bpbwaite/DistributedFenceMonitor/Data Package/Testing/Test Procedures/Board_Power_1.xlsx

Board Number (MKR 1310) | Status | Minimum Current(mA) | Maximum Current(mA) | Accelerometer | Voltage (V) | Current (mA)
A1 | OK | 18 | 111 | (ADXL) 1 | 3.3 | 0.0215
A2 | OK |  |  | (ADXL) 2 | 3.3 | 0.0215
A3 | OK |  |  | (ADXL) 3 | 3.3 | 0.0239
A4 | OK |  |  | (ADXL) 4 | 3.3 | 0.0226
 |  |  |  | (MPU) 5 | 3.3 | 2
 |  |  |  | (MPU) 6 | 3.3 | 1
Board Number (RP2040) |  | Baseline Current(mA) | Max Current(mA) | (MPU) 7 | 3.3 | 2
1 |  | 41 | 120
2 |  | 40 | 120
