bpbwaite/DistributedFenceMonitor/Data Package/Testing/Test Procedures/Capstone Testing Software.xlsx

Software Requirement | Code Portions | Location | Pass/Fail | Notes
setup_mkr1310() run | setup_mkr1310() | dfm_mkr1310.cpp | Pass | Serial.Prints worked and could be seen through the serial monitor
Maximum Scan Loops | while (++attackCounter <= MAXIMUM_SCANS) | dfm_mkr1310.cpp | Fail | Tested if the data collection loop would stop collecting after a set collection time of 10 seconds. Node would not break out of loop after continous motion.
Epoch Timing Test | next_wake_epoch, next_send_epoch | dfm_mkr1310.cpp, | Fail | Timing on each node was incorrect. Node 1 and 2 sent and woke up at the same time without waiting for one to send and the other not to send. Next phase is to calibrate Epoch with identifiers.
Maximum Scan Loops p2 | while (++attackCounter <= MAXIMUM_SCANS) | dfm_mkr1310.cpp | Pass | Added Inactivity in Data End Function that checks last 1/4 second of data and determines if collection should stop after 10 seconds or continue for another 10 seconds. Function caused loop to exit after 10 seconds and 20 seconds of collection
Severity Test | SeverityLevel | dfm_mkr1310.cpp | Fail | Nodes were returning 15 severity on every motion. No sensitivity abstraction from the nodes. This is likely due to the node always choosing the highest peak which is always going to be 15
Severity Test p2 | SeverityLevel=getFilteredSeverity) | dfm_mkr1310.cpp | Pass | After applying a FIR and utilizing a conv on the data, the severity level returned a more accurate severity level for each instance of motion. Calibration is done for FIR in setup. Severity was serial printed.
Motion Wakeup | if(motionDetected) | dfm_mkr1310.cpp | Pass | Final Test for ISR and the nodes wokeup for a motion detection. Successfully sent Serial Print indicating they were in collection mode and printed severity.
Timing Test p2. | next_wake_epoch, next_send_epoch | dfm_mkr1310.cpp | Pass | After applying an identifier with Epoch, each node waits 1 second after the previous node sent data to send theirs. Nodes sleep and wakeup based on their identifier.
