bpbwaite/DistributedFenceMonitor/Data Package/Testing/Test Procedures/Waterproofing Standard.pdf

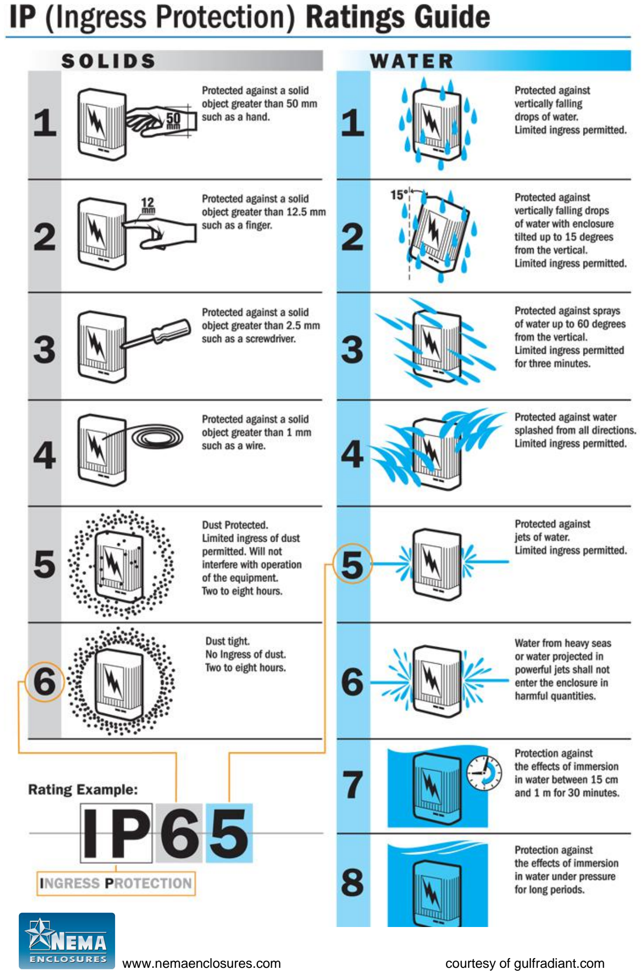
[picture p20: page 1]

www.nemaenclosures.com | courtesy of gulfradiant.com
