bpbwaite/DistributedFenceMonitor/Data Package/Testing/on_fence_testing.xlsx

climb # | unit 1 | unit 3
between units
1 | 7 | 3
2 | 5 | 4
3 | 6 | 5
4 | 10 | 3 | right in the middle, jack
same pannel as unit 1 blue and grey
1 | 15 | 0
2 | 15 | 0
3 | 15 | 0
one pannel away from 1 between 1 and 3
1 | 7 | 0
2 | 11 | 3
3 | 12 | 2
one pannel away from unit 3 between one and three
1 | 3 | 4
2 | 6 | 5 | tried to climb the pole
3 | 0 | 9 | zac
same panel as unit 3
1
2
3
