bpbwaite/DistributedFenceMonitor/interpreter/Power Tests/scope_2.csv

x-axis | 1 | 2
second | Volt | Volt
+1.2200E+00 | +3.2657E+00 | +104.2E-03
+1.2300E+00 | +3.2531E+00 | +103.0E-03
+1.2400E+00 | +3.2330E+00 | +102.4E-03
+1.2500E+00 | +3.2129E+00 | +101.9E-03
+1.2600E+00 | +3.1928E+00 | +100.1E-03
+1.2700E+00 | +3.1853E+00 | +103.9E-03
+1.2800E+00 | +3.2657E+00 | +103.7E-03
+1.2900E+00 | +3.2657E+00 | +102.5E-03
+1.3000E+00 | +3.2582E+00 | +101.9E-03
+1.3100E+00 | -30.8E-03 | +61.7E-03
+1.3200E+00 | -111.2E-03 | +58.3E-03
+1.3300E+00 | -83.5E-03 | +58.0E-03
+1.3400E+00 | -30.8E-03 | +55.1E-03
+1.3500E+00 | -43.3E-03 | +61.5E-03
+1.3600E+00 | -30.8E-03 | +59.9E-03
+1.3700E+00 | -111.2E-03 | +59.6E-03
+1.3800E+00 | -38.3E-03 | +60.9E-03
+1.3900E+00 | -43.3E-03 | +58.0E-03
+1.4000E+00 | -30.8E-03 | +59.3E-03
+1.4100E+00 | -30.8E-03 | +58.6E-03
+1.4200E+00 | -38.3E-03 | +59.8E-03
+1.4300E+00 | -30.8E-03 | +58.5E-03
+1.4400E+00 | -30.8E-03 | +60.3E-03
+1.4500E+00 | -58.4E-03 | +58.0E-03
+1.4600E+00 | -103.6E-03 | +59.3E-03
+1.4700E+00 | -43.3E-03 | +58.3E-03
+1.4800E+00 | -111.2E-03 | +57.3E-03
+1.4900E+00 | -83.5E-03 | +55.9E-03
+1.5000E+00 | -111.2E-03 | +58.2E-03
+1.5100E+00 | -111.2E-03 | +57.1E-03
+1.5200E+00 | -63.4E-03 | +57.7E-03
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
