bpbwaite/DistributedFenceMonitor/include/dfm_errors.h

/*
  FILE: DFM_ERRORS.H
  VERSION: 1.0.0
  DATE: 27 March 2023
  PROJECT: Distributed Fence Monitor Capstone
  AUTHORS: Briellyn Braithwaite
  DESCRIPTION:
*/
#pragma once

#define ERROR_NO_SERIAL 0b00101000
#define ERROR_ADXL345   0b10011100
#define ERROR_NO_LORA   0b11000010
#define ERROR_BAD_ALLOC 0b10101010
