bpbwaite/DistributedFenceMonitor/include/dfm_recv_mkr1310.h

/*
  FILE: DFM_RECV_MKR1310.H
  VERSION: 0.0.1
  DATE: 6 February 2023
  PROJECT: Distributed Fence Monitor Capstone
  AUTHORS: Briellyn Braithwaite
  DESCRIPTION: Refer to DFM_MKR1310.H for details
*/
#pragma once

#ifdef ARDUINO_SAMD_MKRWAN1310

#include "dfm_mkr1310.h"

void setup_recv_mkr1310();
void loop_recv_mkr1310();
#endif
